42CrMo4/96-Well_Pipette_visualizer/SW/SW-P00C/matrix.h

// matrix.h
#ifndef MATRIX_H
#define MATRIX_H

const int rows = 8;
const int cols = 12;

int matrix[rows][cols] = 
{
  {84, 85, 86, 87, 88, 89, 90, 91, 92, 93, 94, 95},
  {83, 82, 81, 80, 79, 78, 77, 76, 75, 74, 73, 72},
  {60, 61, 62, 63, 64, 65, 66, 67, 68, 69, 70, 71},
  {59, 58, 57, 56, 55, 54, 53, 52, 51, 50, 49, 48},
  {36, 37, 38, 39, 40, 41, 42, 43, 44, 45, 46, 47},
  {35, 34, 33, 32, 31, 30, 29, 28, 27, 26, 25, 24},
  {12, 13, 14, 15, 16, 17, 18, 19, 20, 21, 22, 23},
  {11, 10,  9,  8,  7,  6,  5,  4,  3,  2,  1,  0}
};

#endif
